ahl/cali-map/out/p0_map_area_relief.png

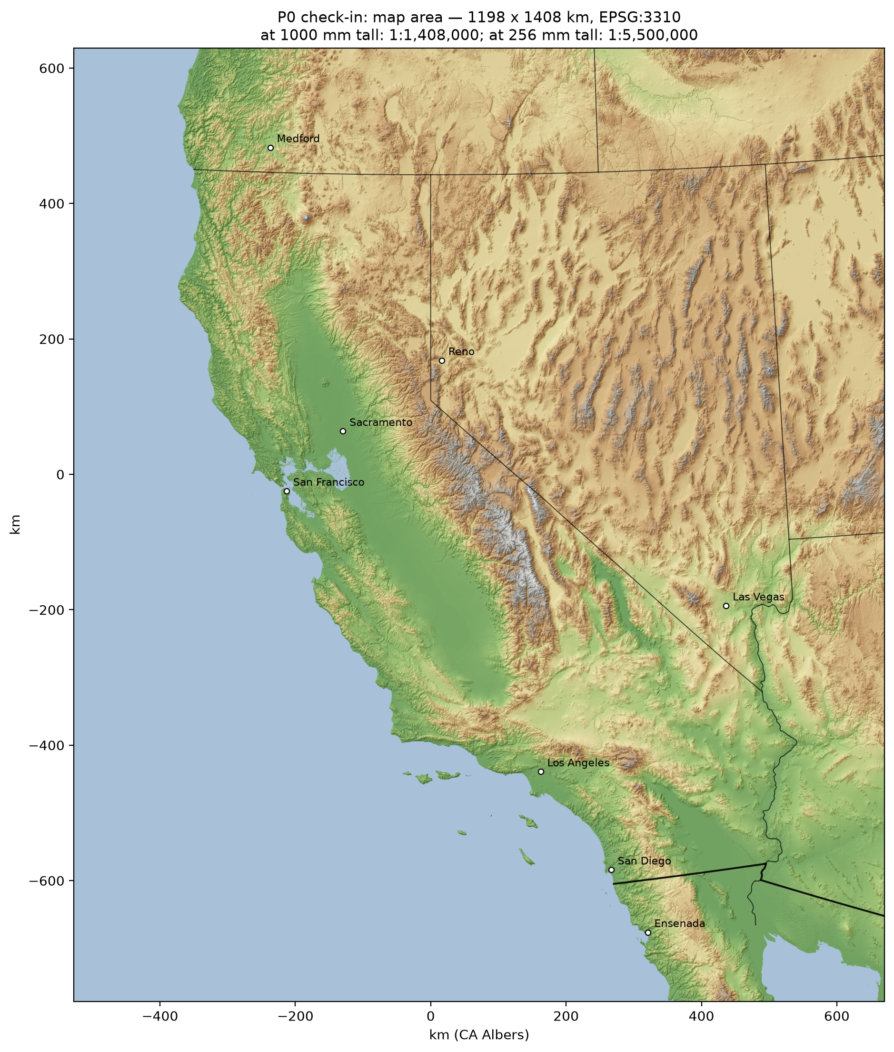
out/p0_map_area_relief.png
