ahl/cali-map/out/p1_coast_candidates.png

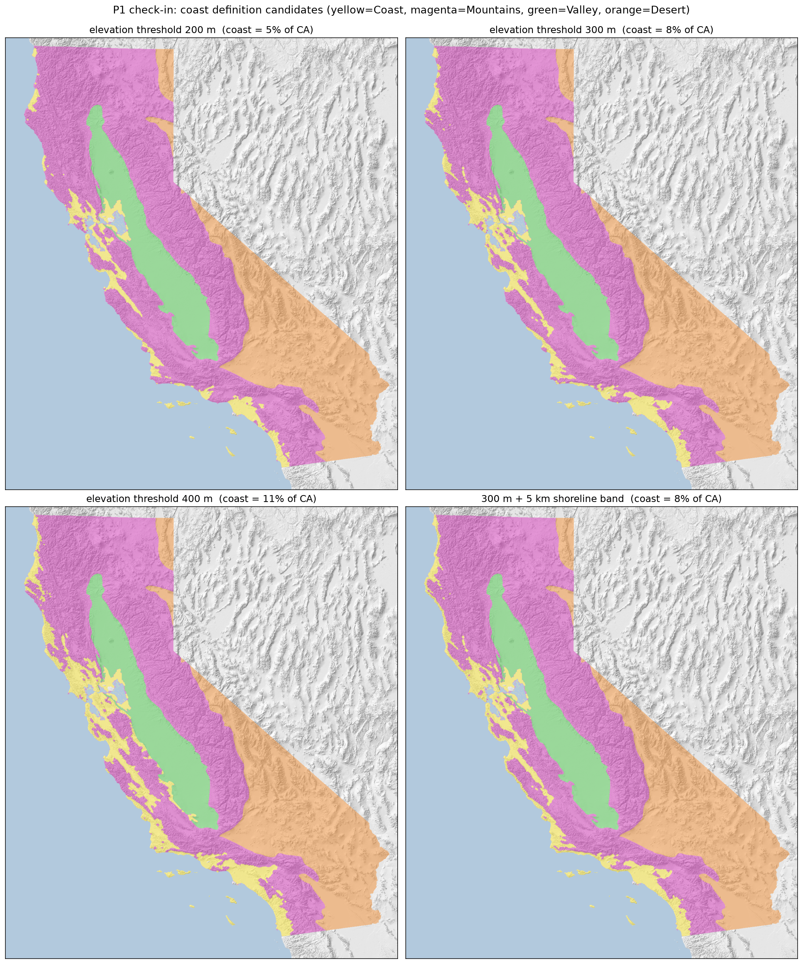
out/p1_coast_candidates.png
