ahl/cali-map/out/p1_final.png

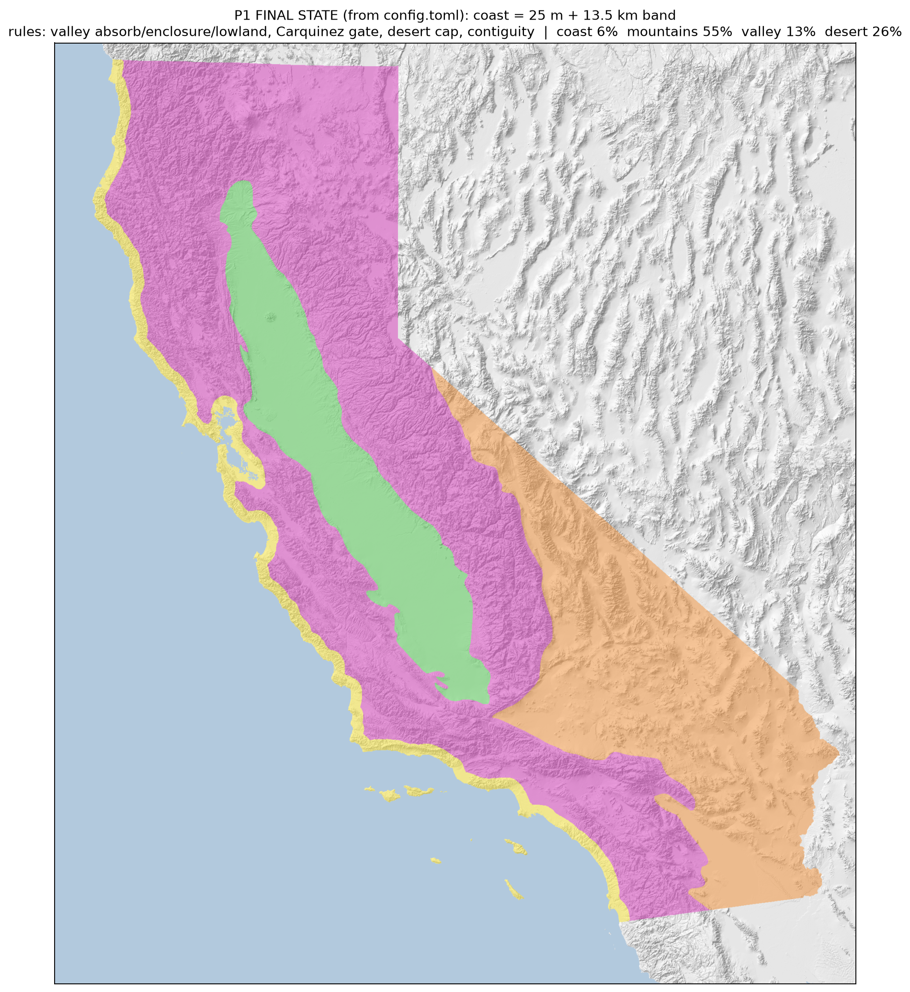
out/p1_final.png
