ahl/cali-map/out/p1a_coast_simplified.png

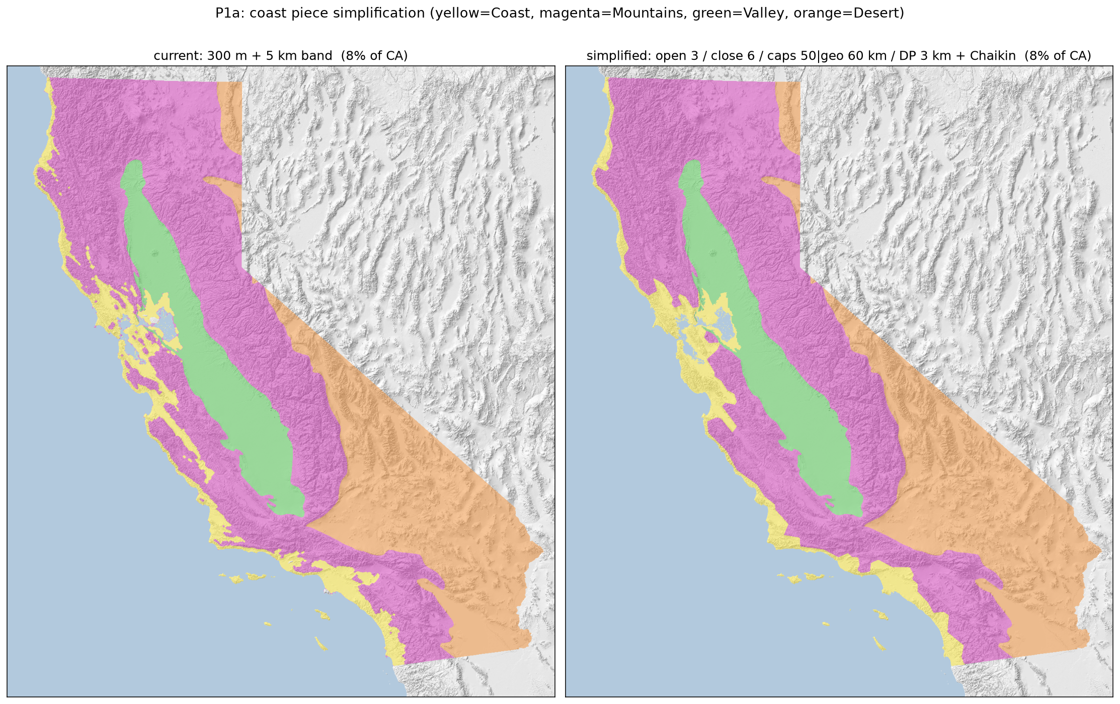
out/p1a_coast_simplified.png
