ahl/cali-map/out/p1b_coast_from_image.png

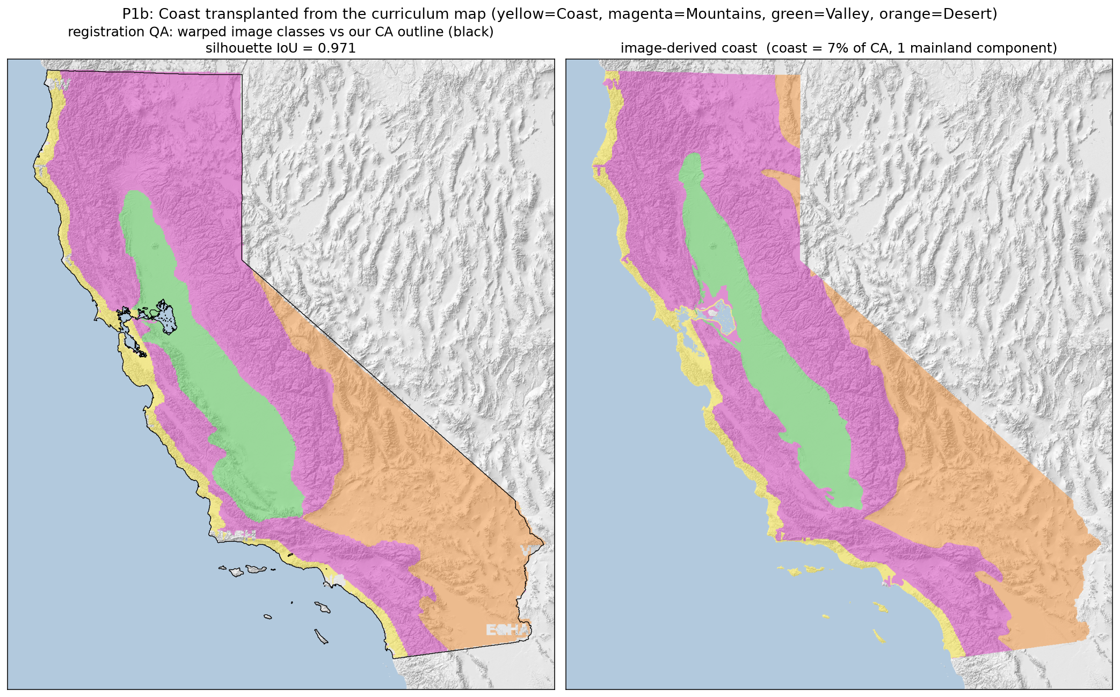
out/p1b_coast_from_image.png
