ahl/cali-map/out/p1d_combined.png

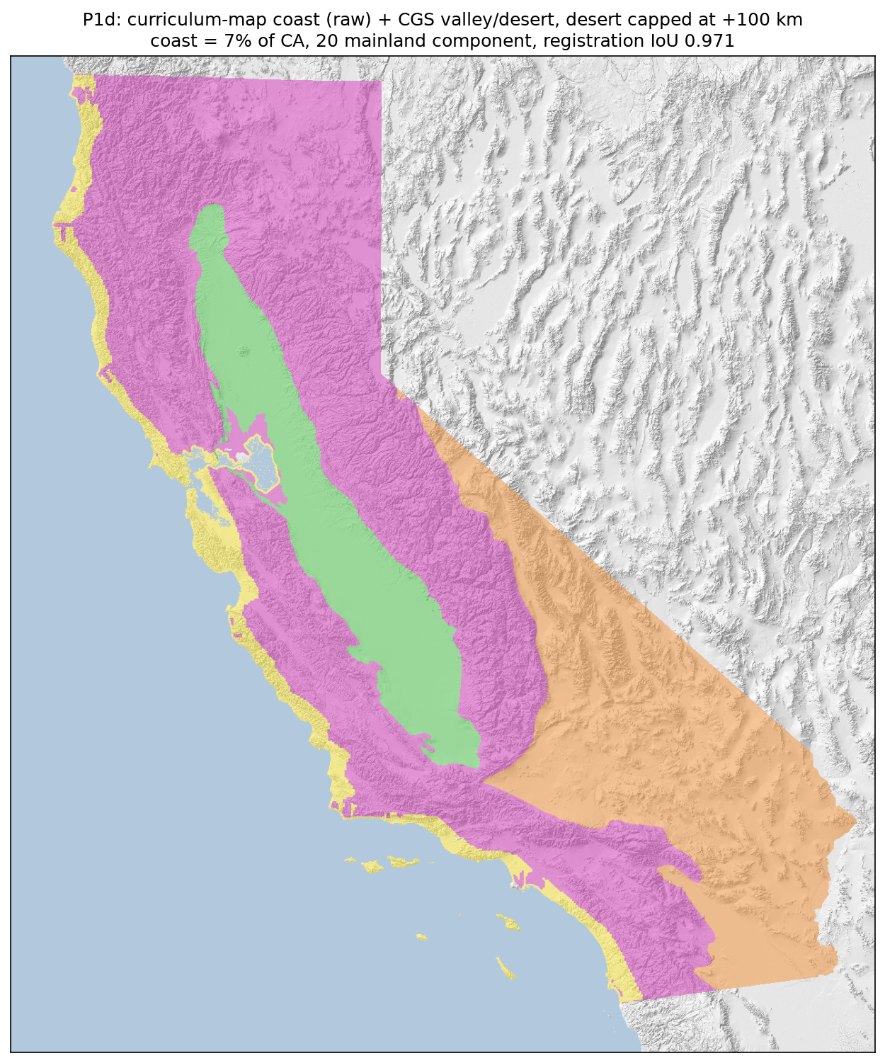
out/p1d_combined.png
