ahl/cali-map/out/p1e_island_buffers.png

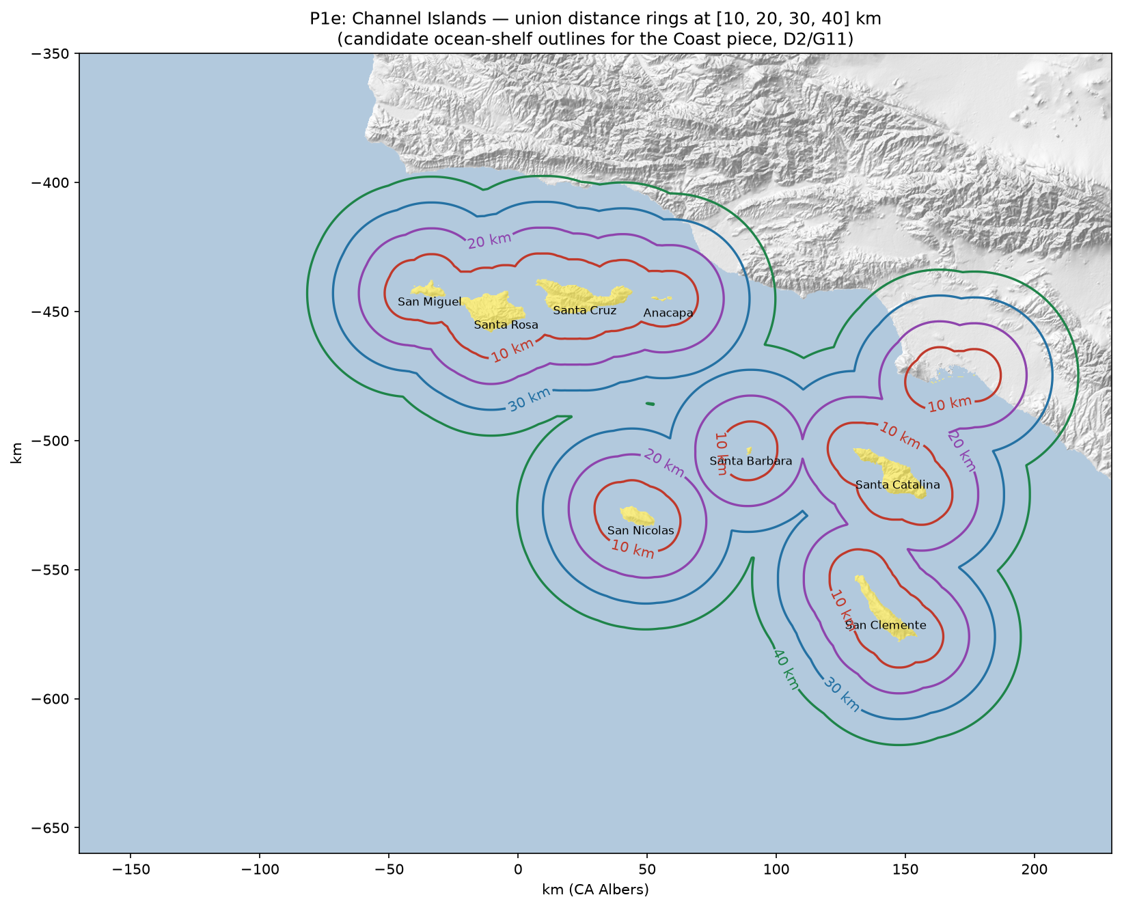
out/p1e_island_buffers.png
