ahl/cali-map/out/p1f_islands_one_piece.png

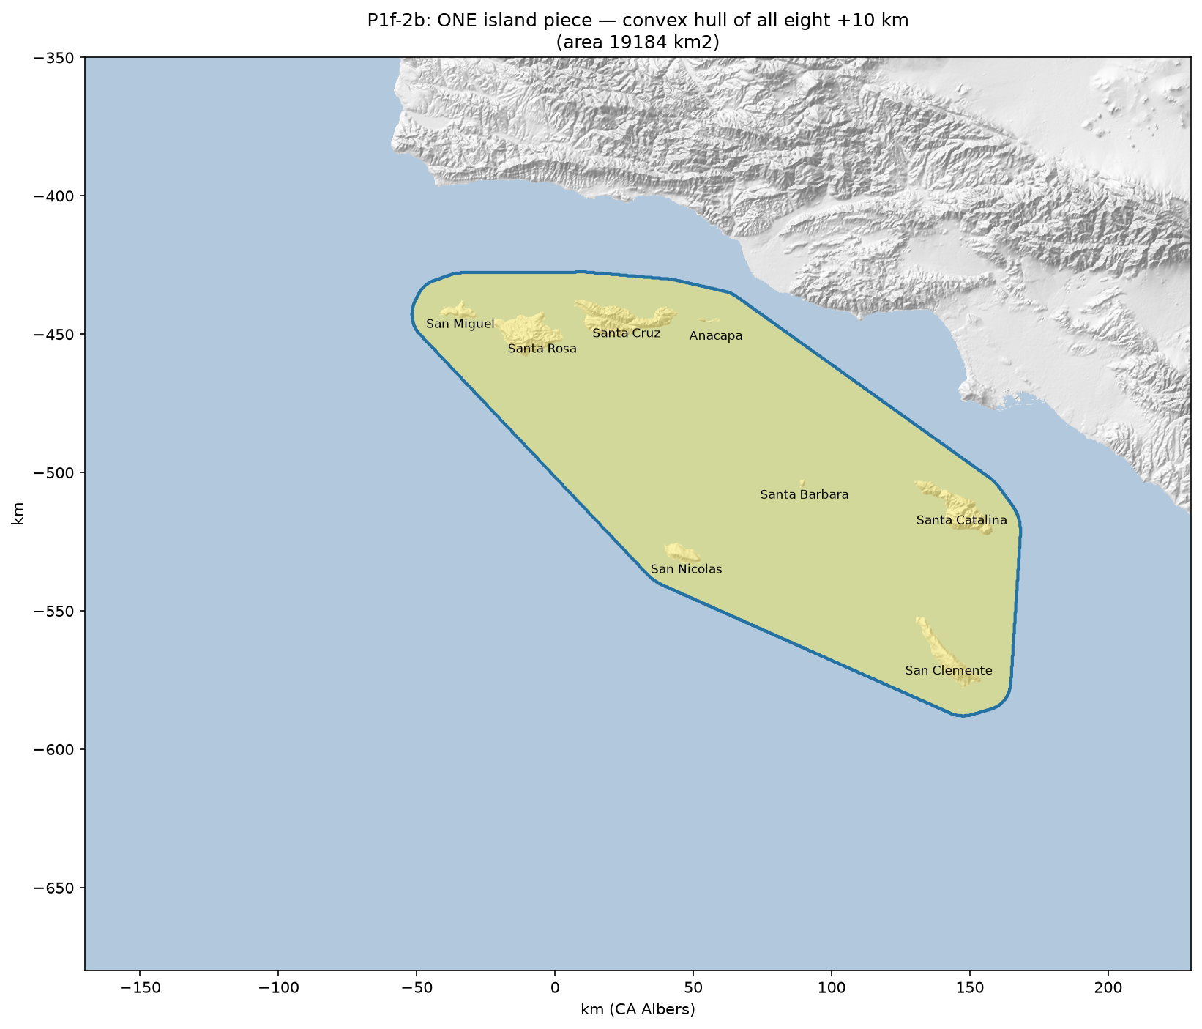
out/p1f_islands_one_piece.png
