ahl/cali-map/out/p1f_islands_two_pieces.png

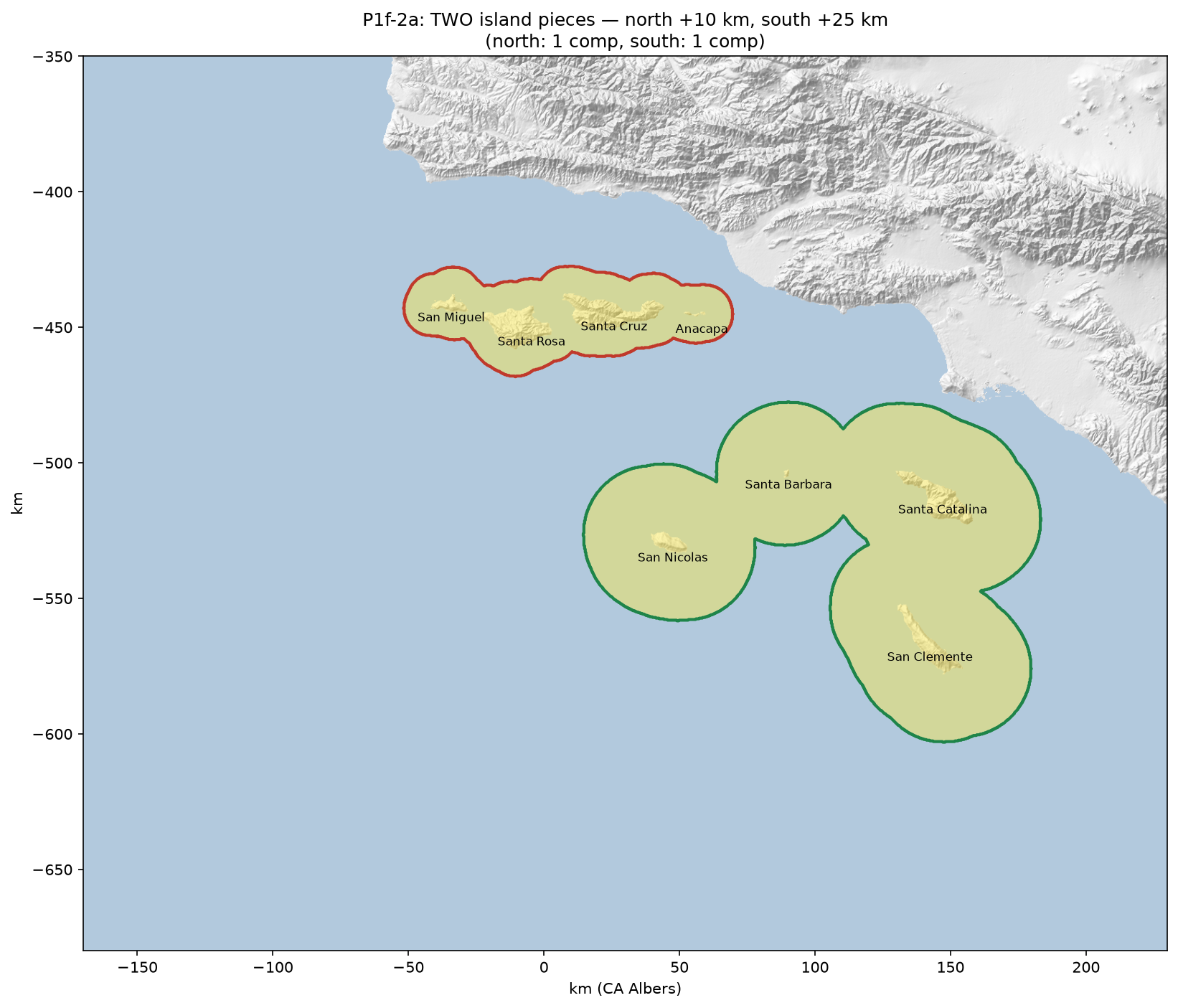
out/p1f_islands_two_pieces.png
