ahl/cali-map/out/p2_layout.png

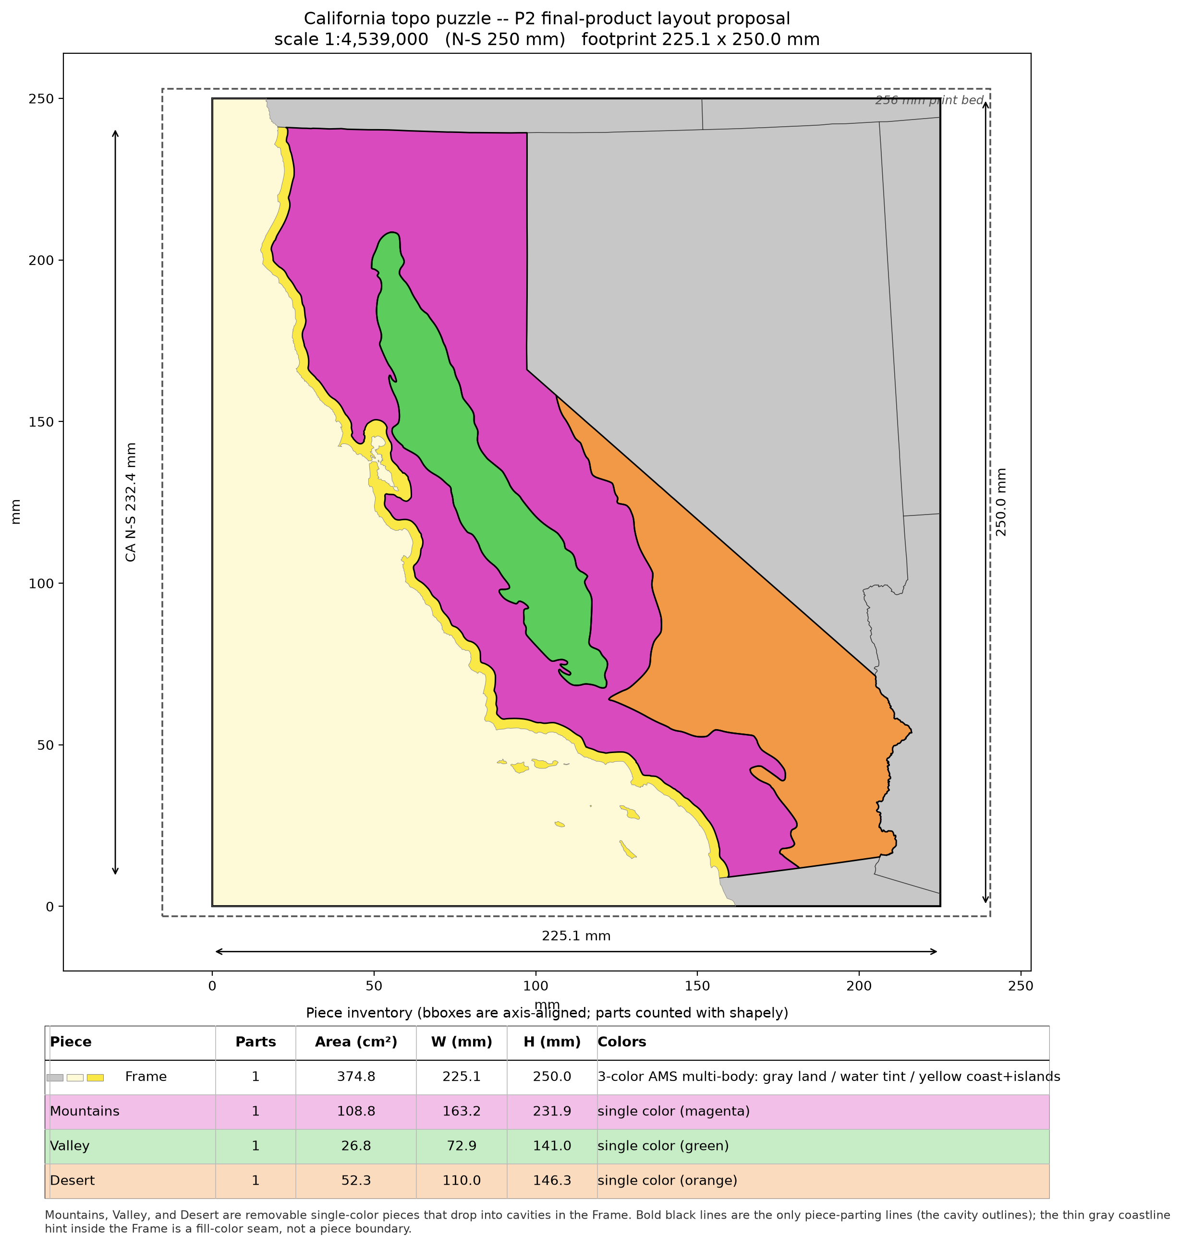
out/p2_layout.png
