ahl/cali-map/out/p2_waterways_preview.png

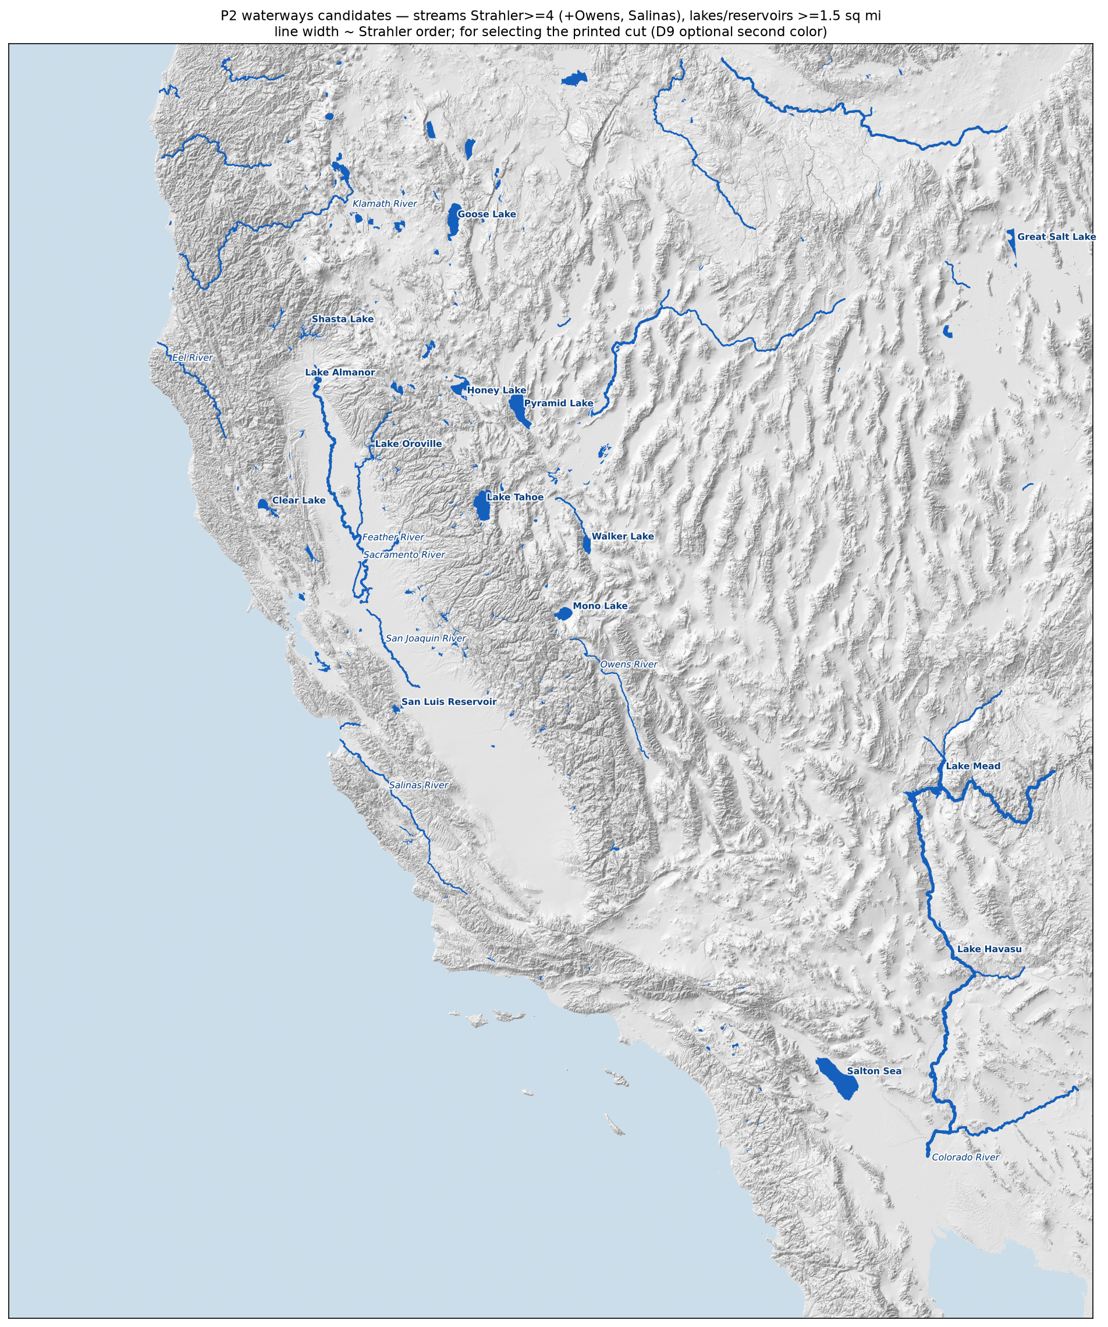
out/p2_waterways_preview.png
