ahl/cali-map/out/p4_preview.png

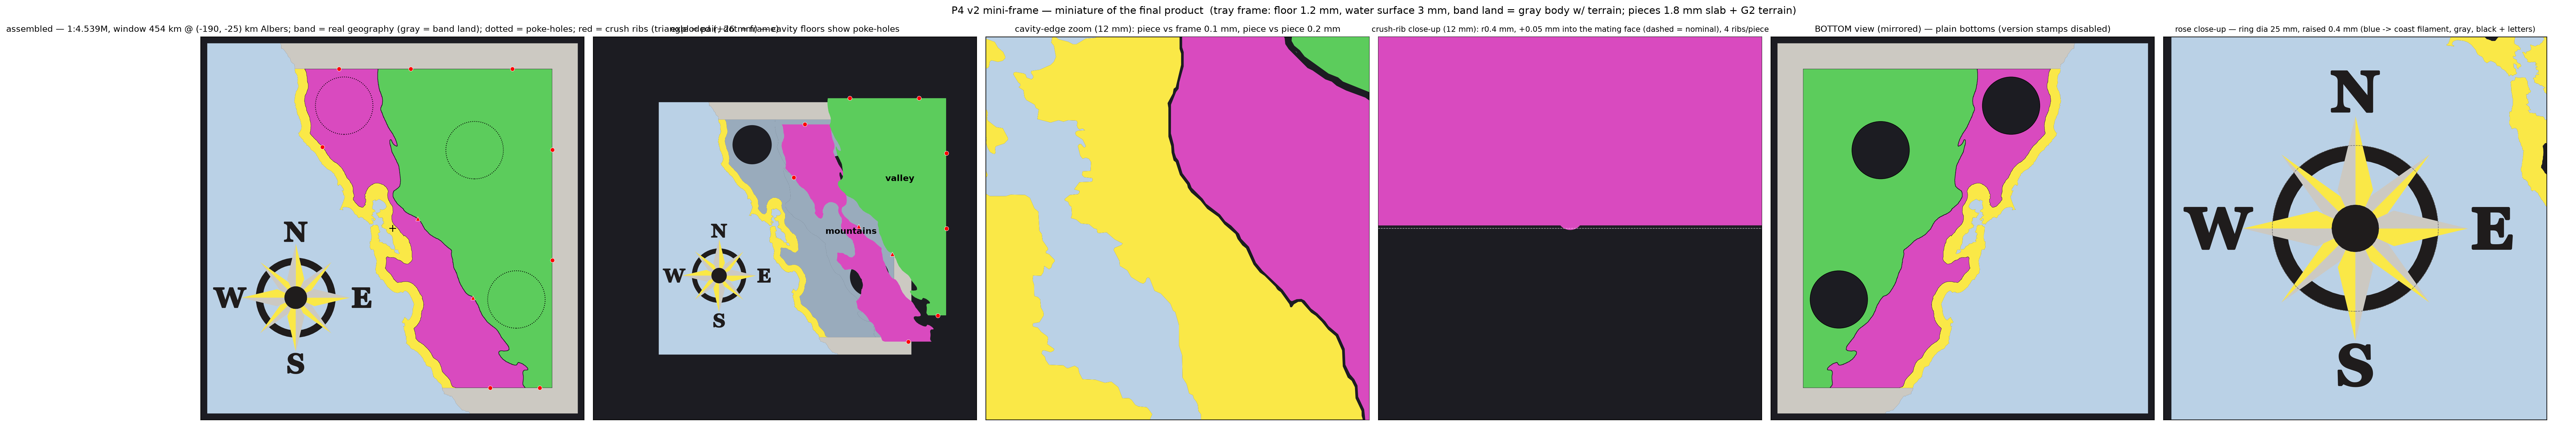
out/p4_preview.png
