ahl/cali-map/out/p4_rib_markup.png

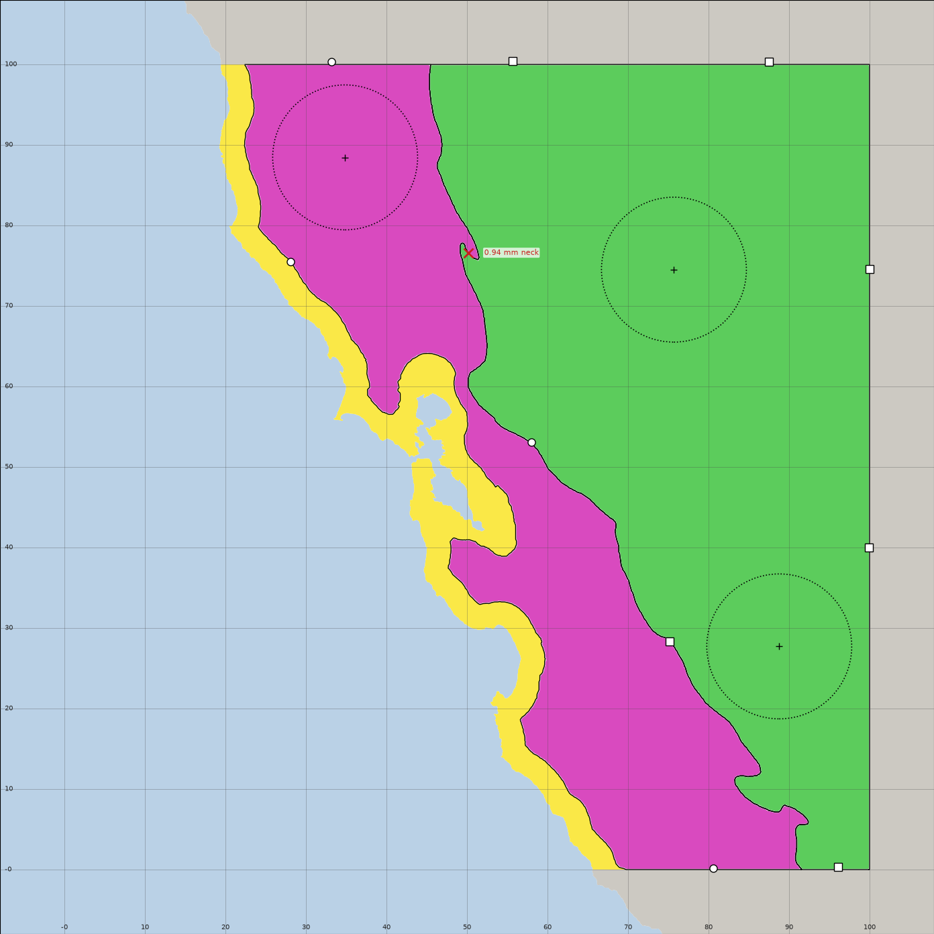
out/p4_rib_markup.png
