ahl/cali-map/out/p5_preview.png

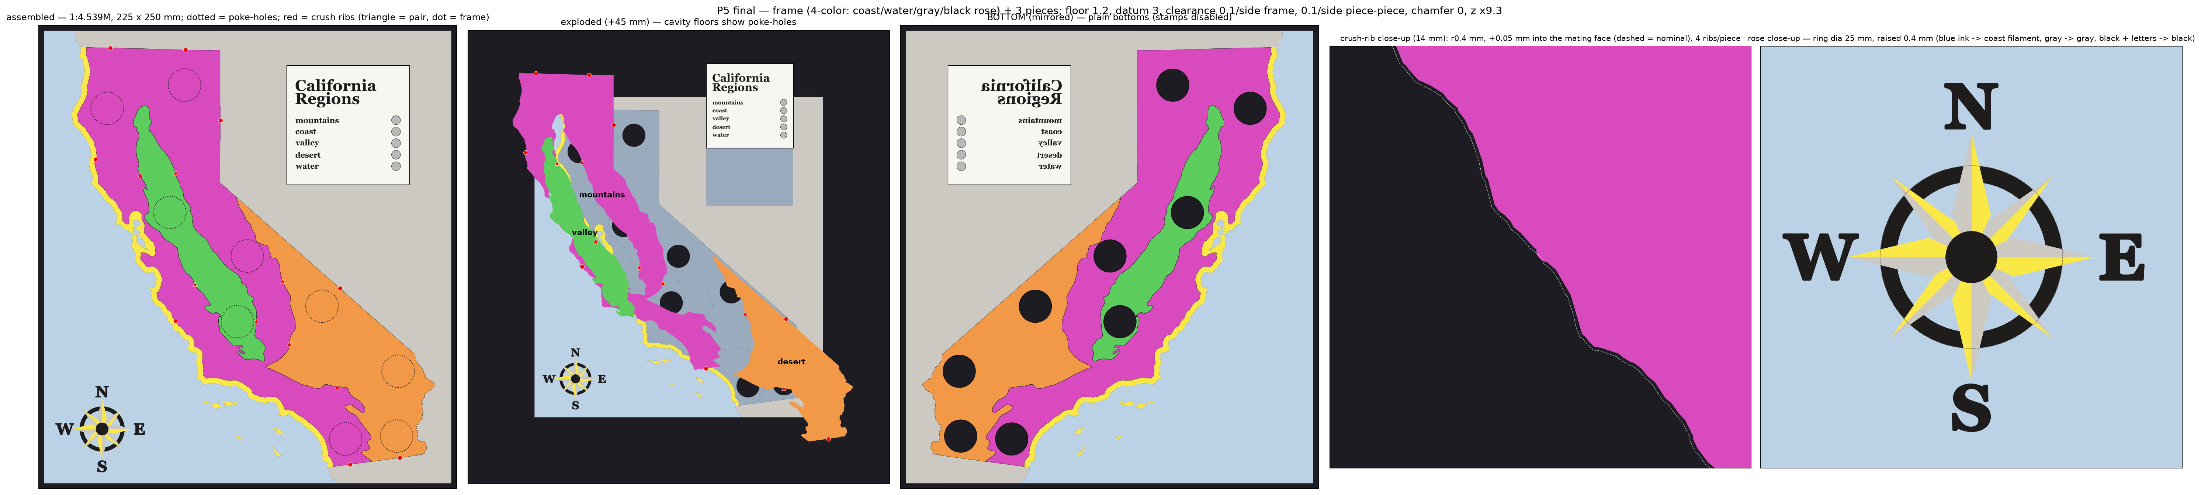
out/p5_preview.png
