ahl/cali-map/out/p5_rib_markup.png

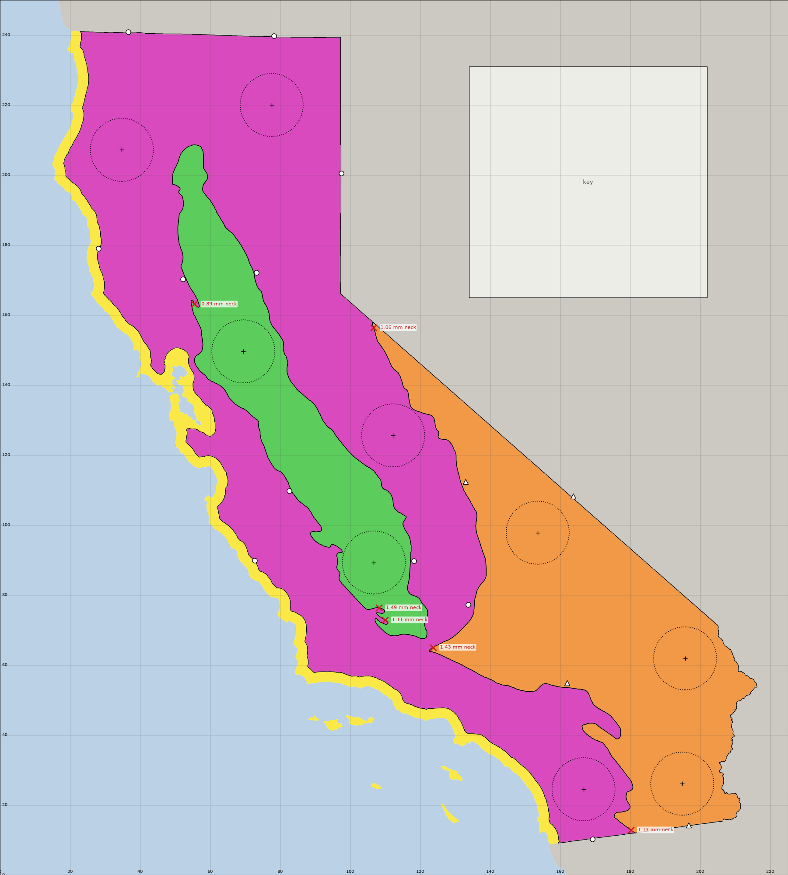
out/p5_rib_markup.png
