ahl/cali-map/out/p15_preview.png

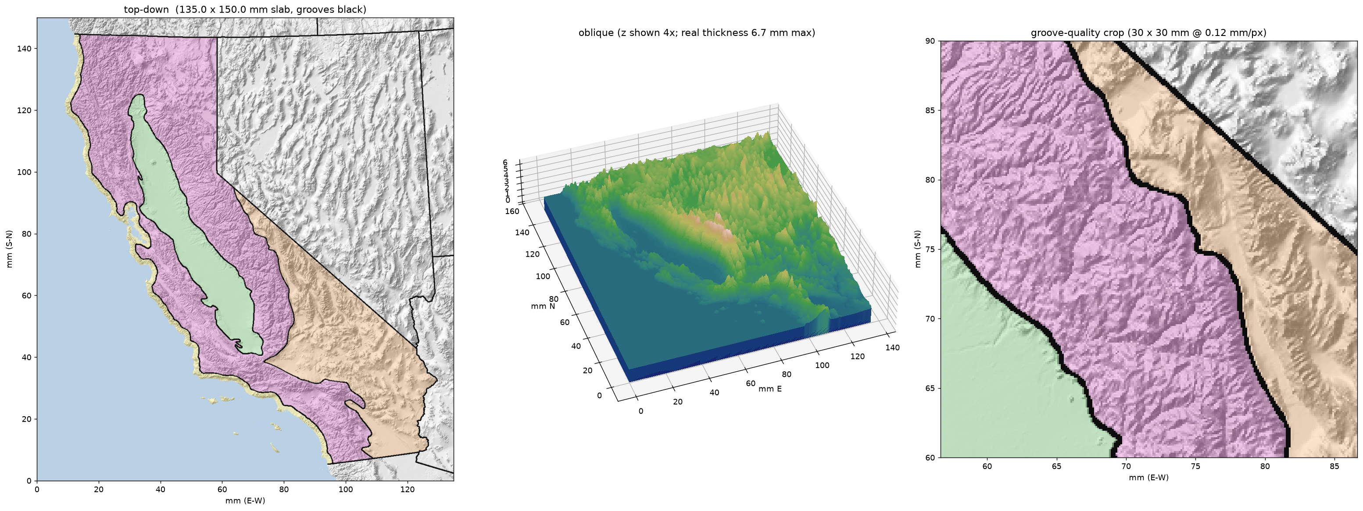
out/p15_preview.png
