ahl/cali-map/out/p15b_preview.png

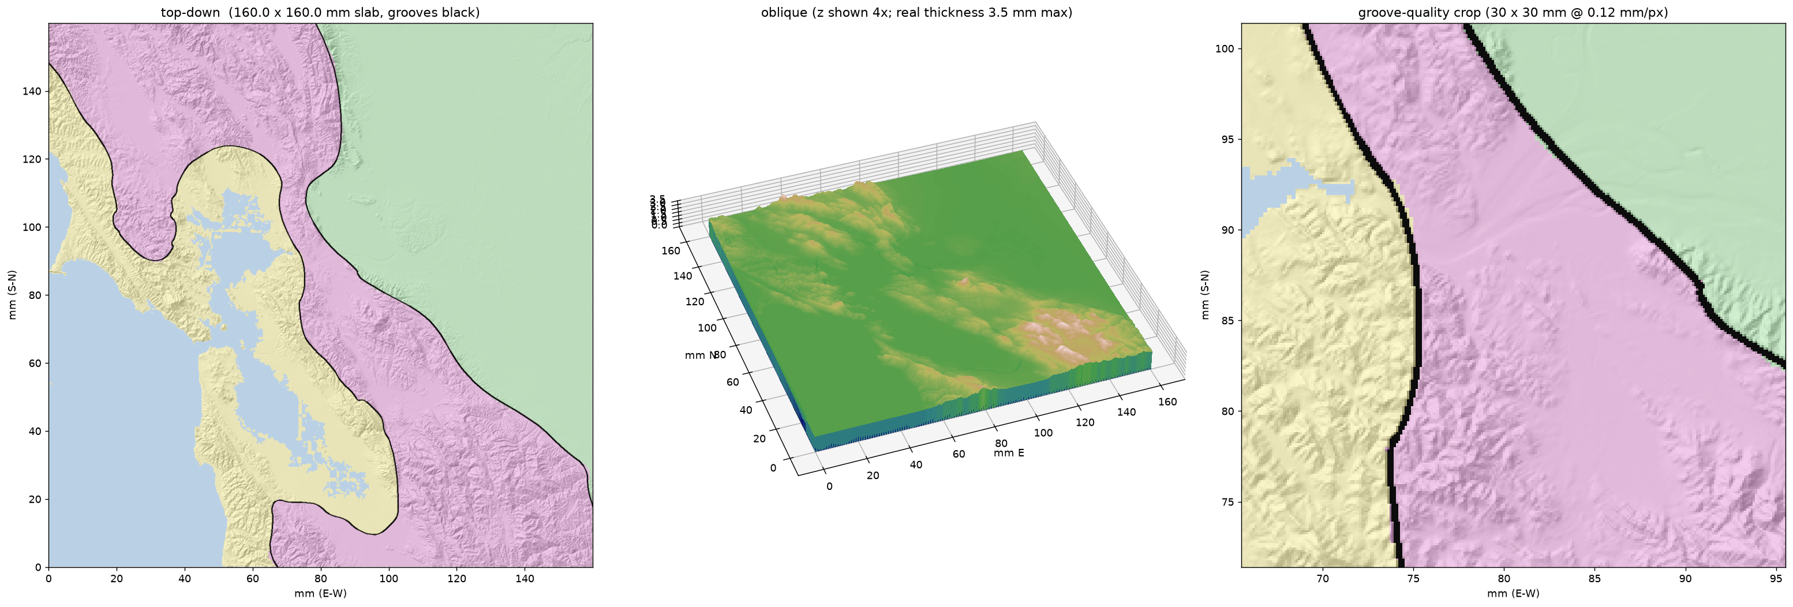
out/p15b_preview.png
