ahl/cali-map/out/p15b_res_compare.png

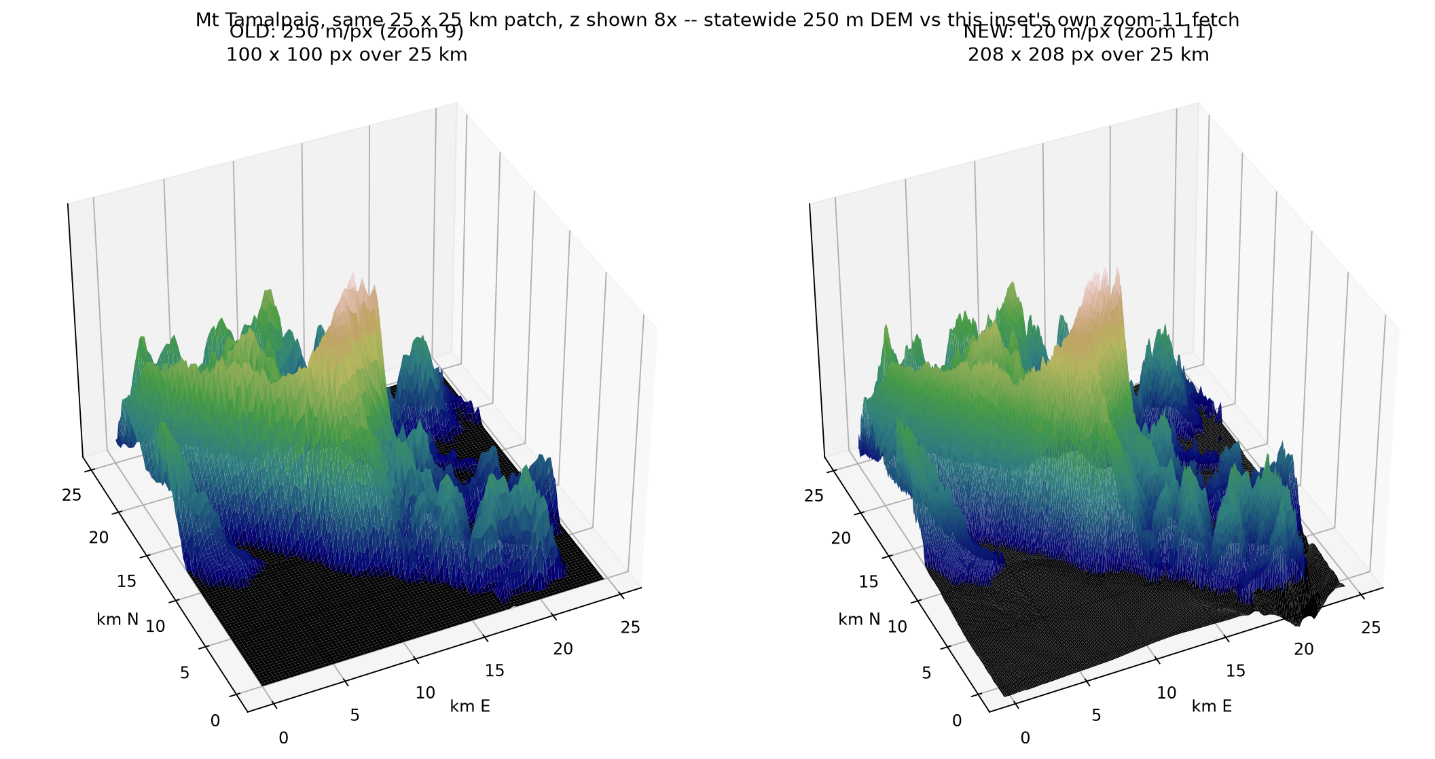
out/p15b_res_compare.png
