ahl/cali-map/out/region_markup.png

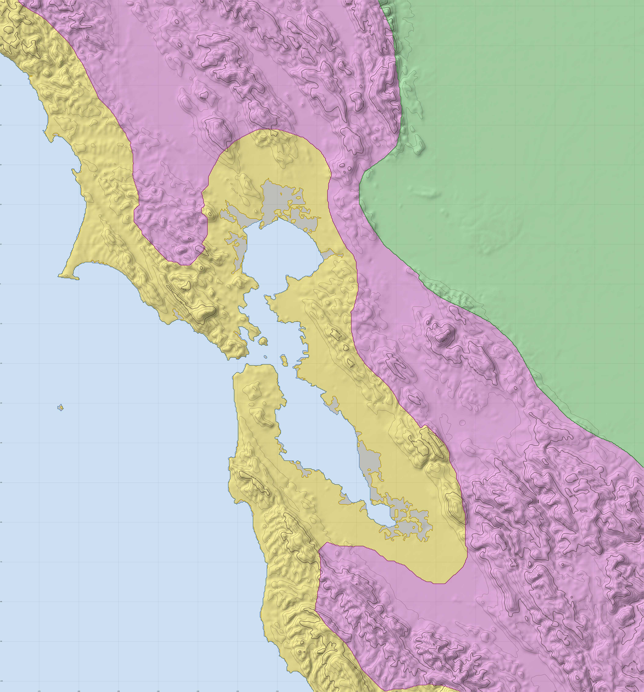
out/region_markup.png
