ahl/cali-map/out/rose_coupon/preview.png

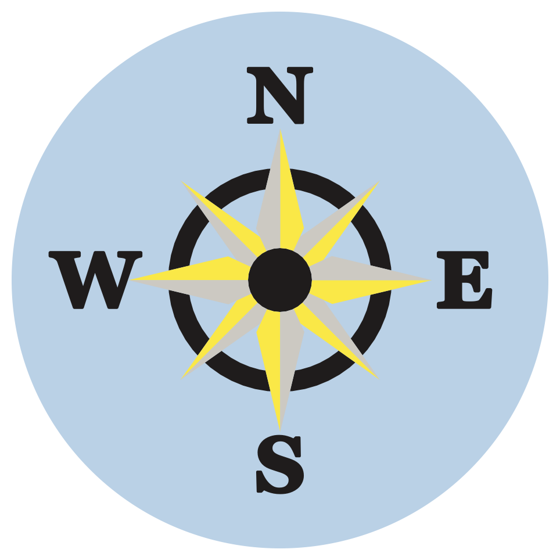
out/rose_coupon/preview.png
