ahl/cali-map/out/p2_land_qa.png

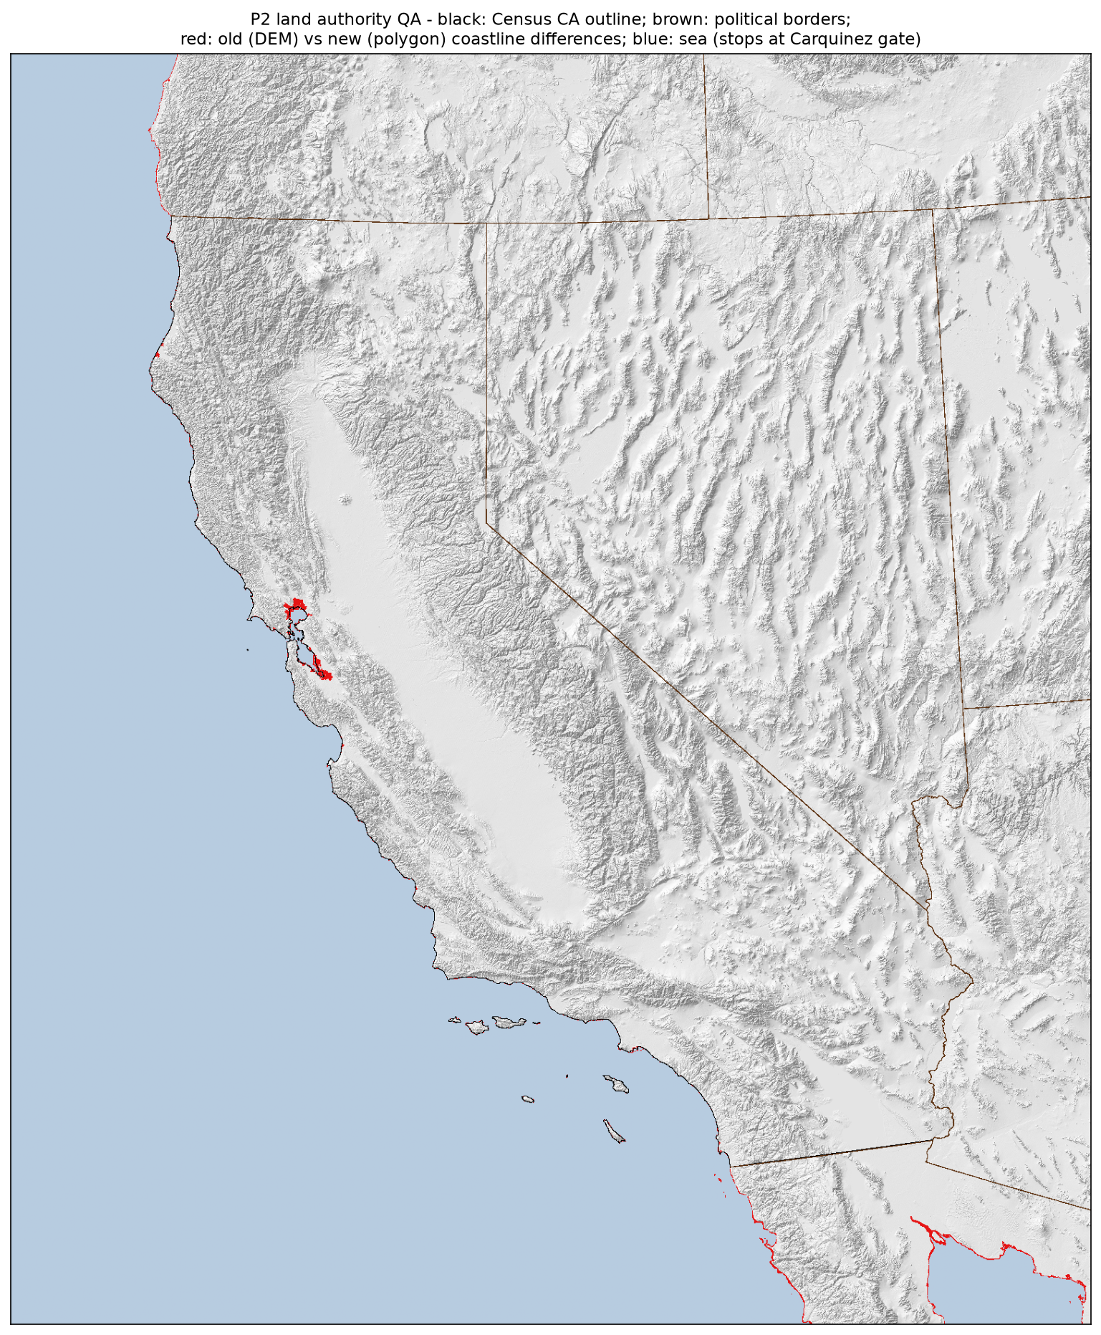
out/p2_land_qa.png
