ahl/cali-map/out/p2_regions_qa.png

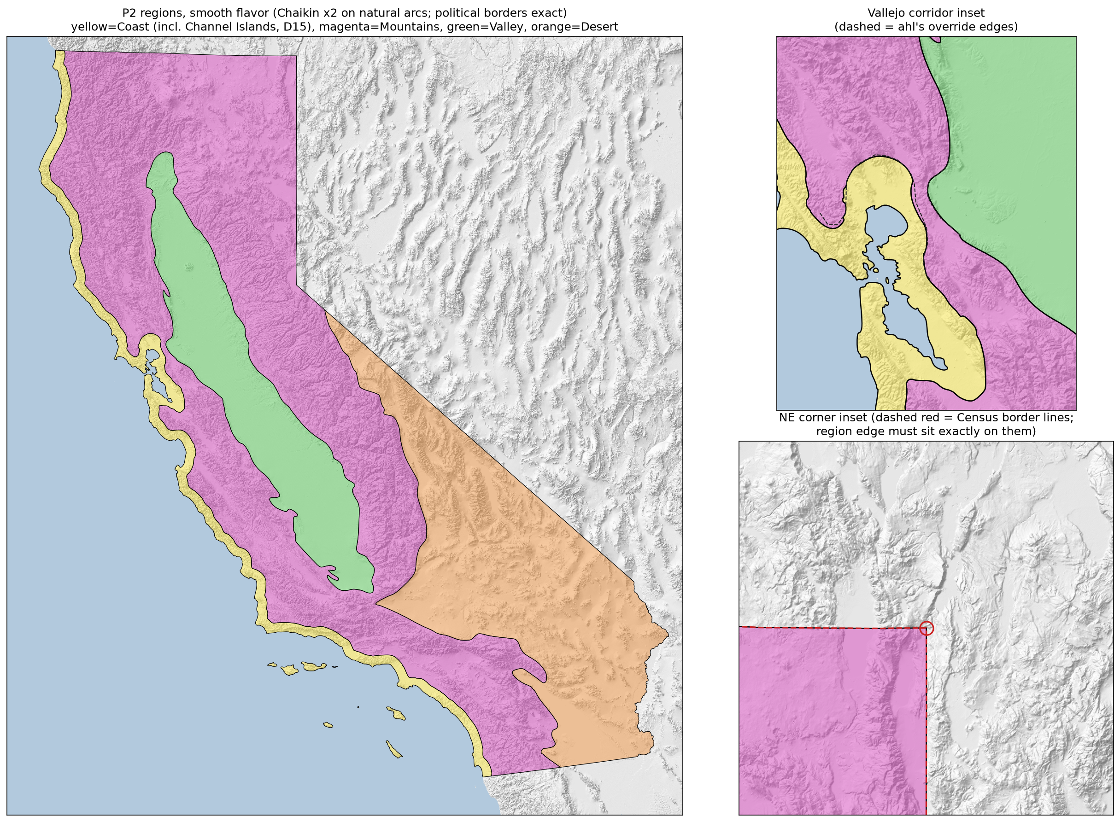
out/p2_regions_qa.png
